Waldehyd/Blahaj_Pentagramm_Badge/Manual/SetupGuide/Images/Real/PartsOverview.jpeg

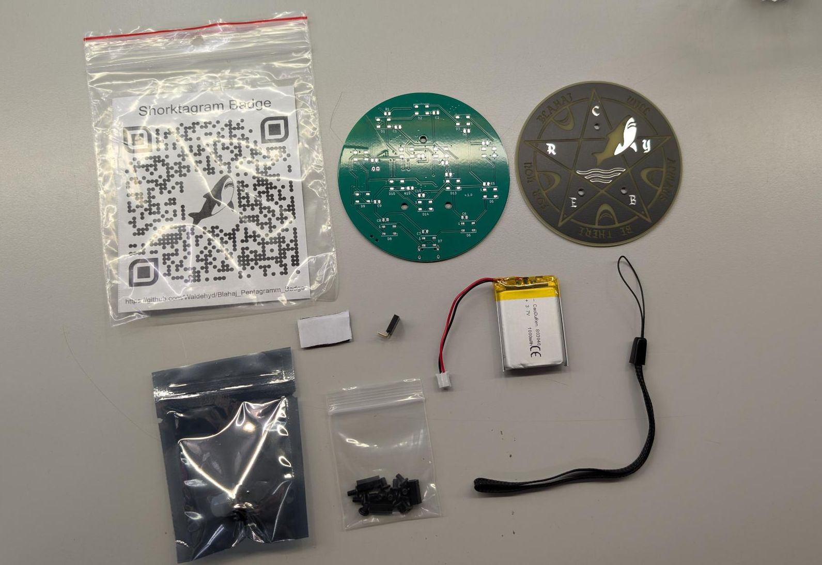
Manual/SetupGuide/Images/Real/PartsOverview.jpeg
