Waldehyd/Blahaj_Pentagramm_Badge/Manual/SetupGuide/Images/CaseScrew.png

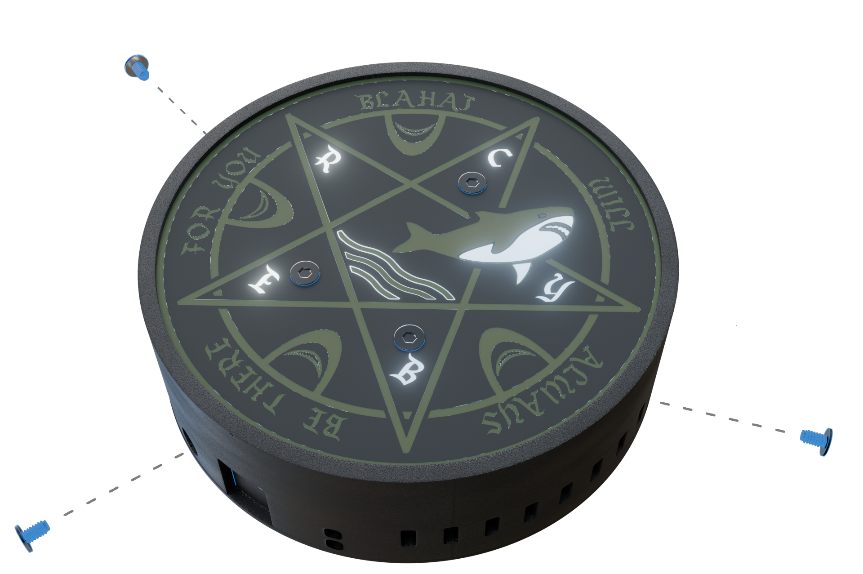
Manual/SetupGuide/Images/CaseScrew.png
