Waldehyd/Blahaj_Pentagramm_Badge/Manual/SetupGuide/Images/Front.png

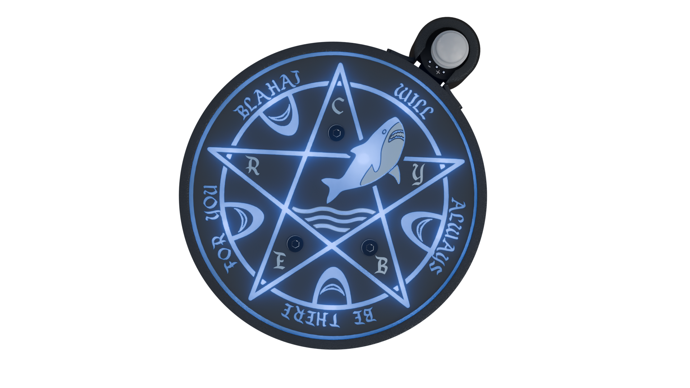
Manual/SetupGuide/Images/Front.png
