Waldehyd/Blahaj_Pentagramm_Badge/Manual/SetupGuide/Images/Fullcase.png

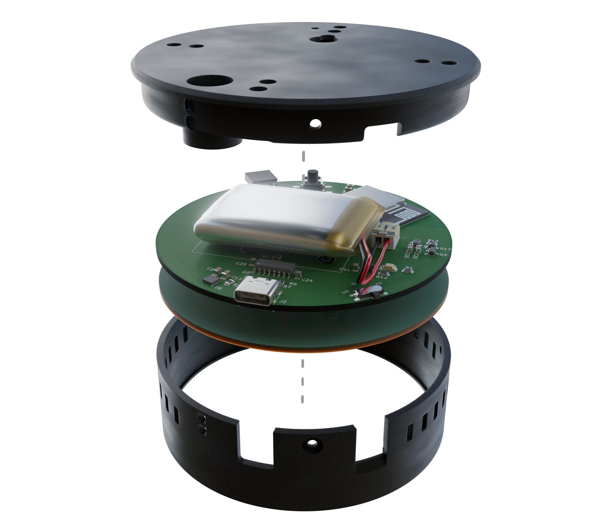
Manual/SetupGuide/Images/Fullcase.png
