Waldehyd/Blahaj_Pentagramm_Badge/Manual/SetupGuide/Images/Mount.png

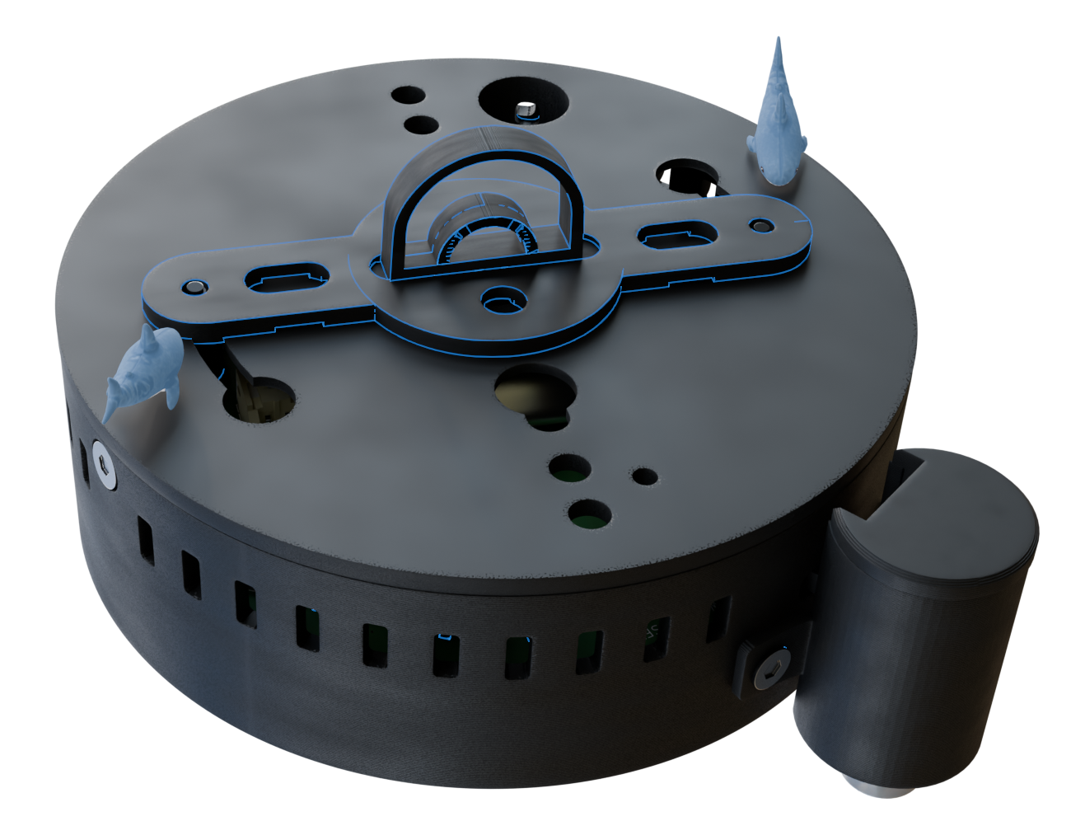
Manual/SetupGuide/Images/Mount.png
