Waldehyd/Blahaj_Pentagramm_Badge/Manual/SetupGuide/Images/MountScrew.png

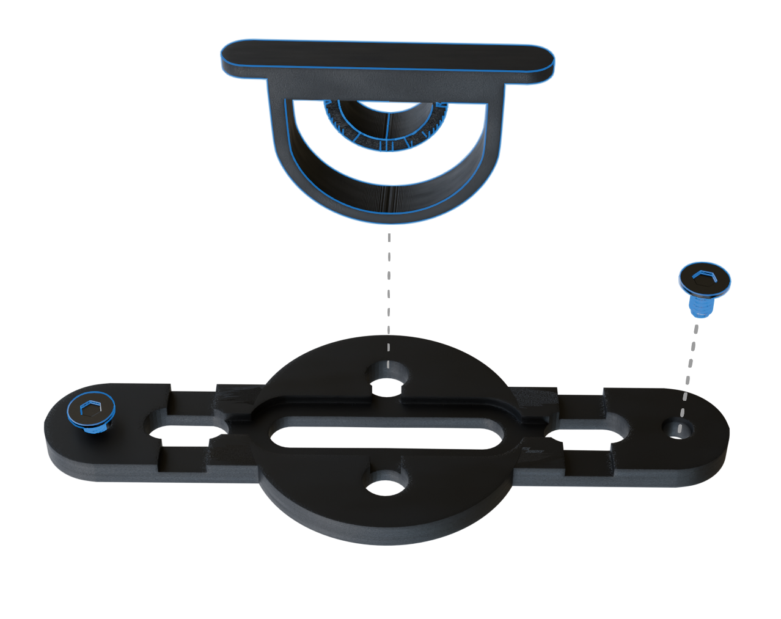
Manual/SetupGuide/Images/MountScrew.png
