Waldehyd/Blahaj_Pentagramm_Badge/Manual/SetupGuide/Images/MQTT.png

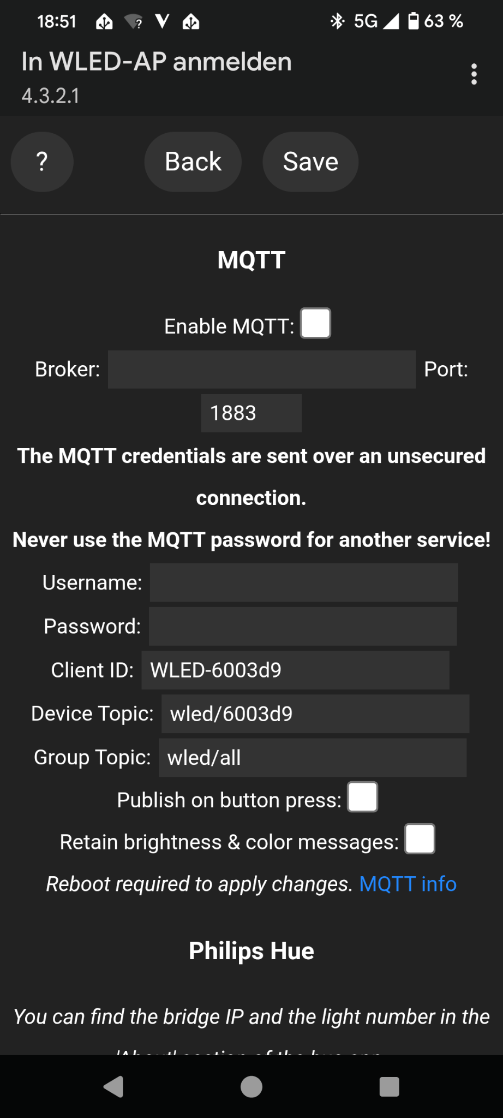
Manual/SetupGuide/Images/MQTT.png
