Waldehyd/Blahaj_Pentagramm_Badge/Manual/SetupGuide/Images/Real/Clamp2.jpeg

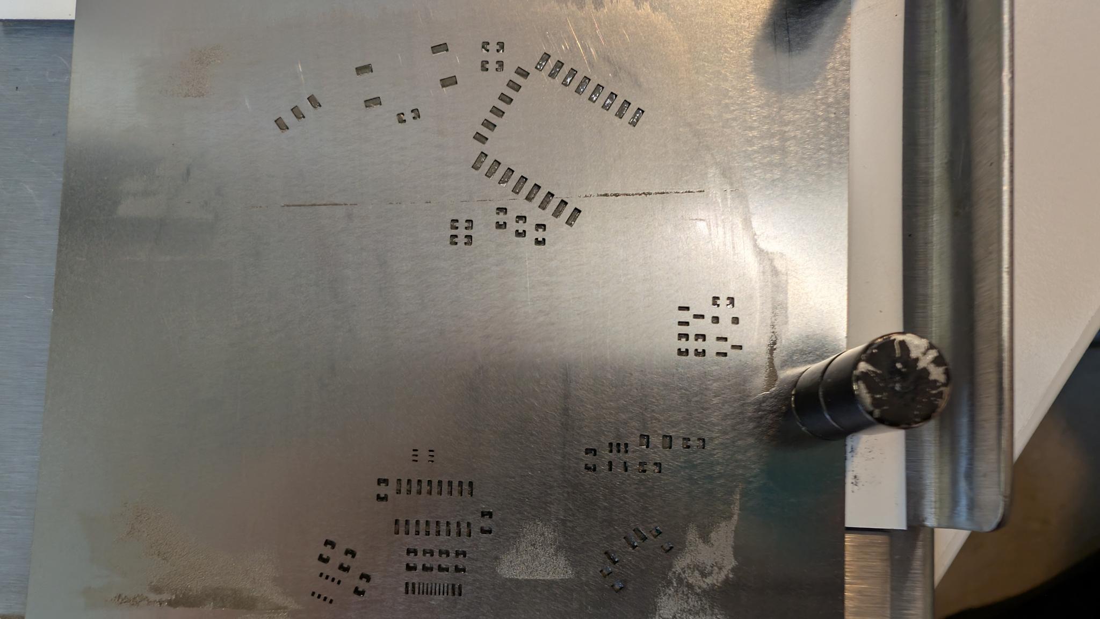
Manual/SetupGuide/Images/Real/Clamp2.jpeg
