Waldehyd/Blahaj_Pentagramm_Badge/Manual/SetupGuide/Images/Real/Paste2.jpeg

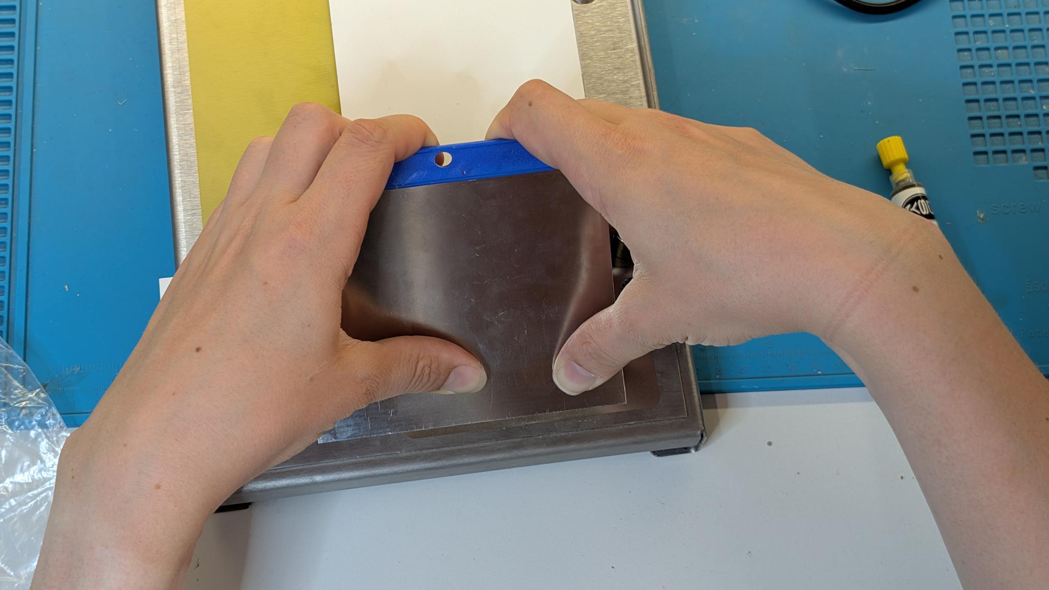
Manual/SetupGuide/Images/Real/Paste2.jpeg
