Waldehyd/Blahaj_Pentagramm_Badge/Manual/SetupGuide/Images/Real/Paste.jpeg

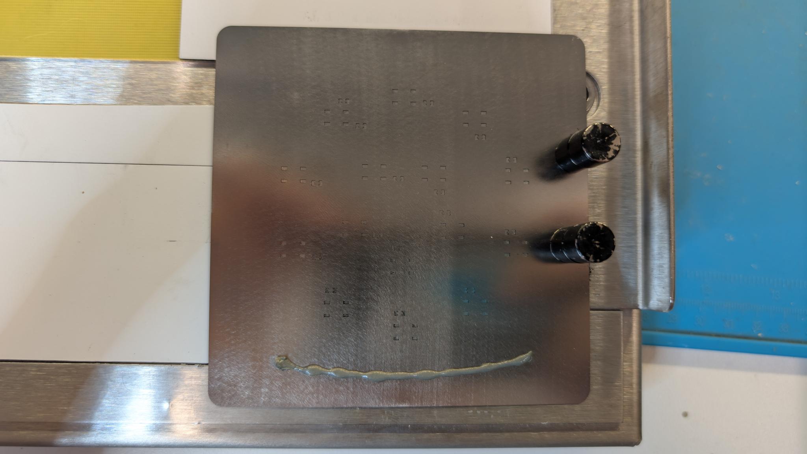
Manual/SetupGuide/Images/Real/Paste.jpeg
