Waldehyd/Blahaj_Pentagramm_Badge/Manual/SetupGuide/Images/Real/signal-2025-08-25-165027_018.jpeg

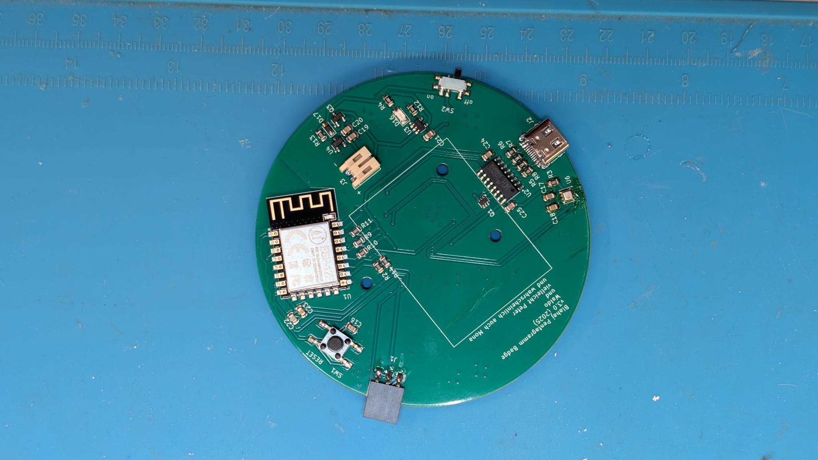
Manual/SetupGuide/Images/Real/signal-2025-08-25-165027_018.jpeg
