Waldehyd/Blahaj_Pentagramm_Badge/Manual/SetupGuide/Images/SensorScrewToCase.png

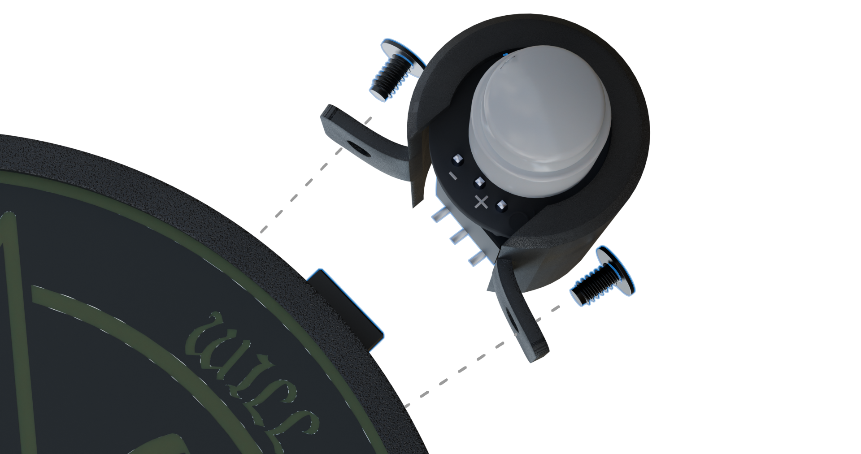
Manual/SetupGuide/Images/SensorScrewToCase.png
