Waldehyd/Blahaj_Pentagramm_Badge/Manual/SetupGuide/Images/Settings.png

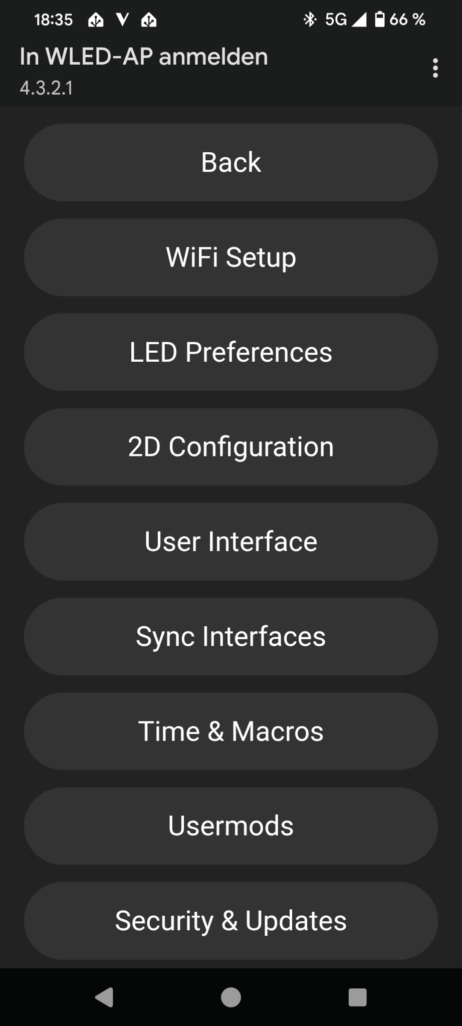
Manual/SetupGuide/Images/Settings.png
