Waldehyd/Blahaj_Pentagramm_Badge/Manual/SetupGuide/Images/Velcro.png

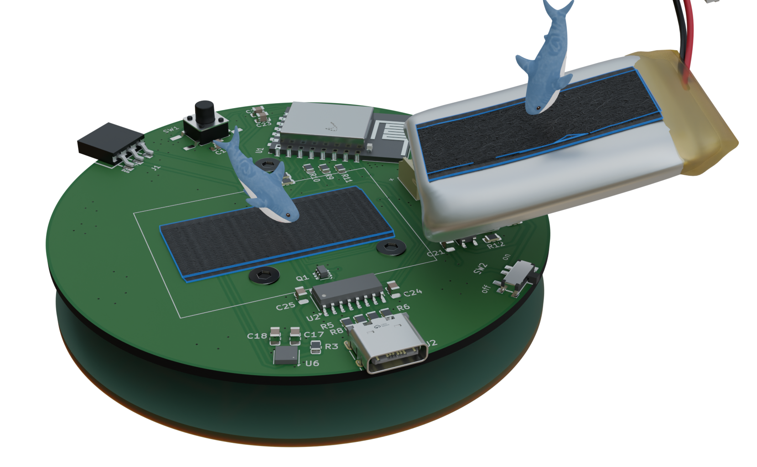
Manual/SetupGuide/Images/Velcro.png
